MOSH-Insa-Toulouse/2023-2024-GP-Delpech_Maurel-Audry/images/Freq coupure 2eme etage.PNG

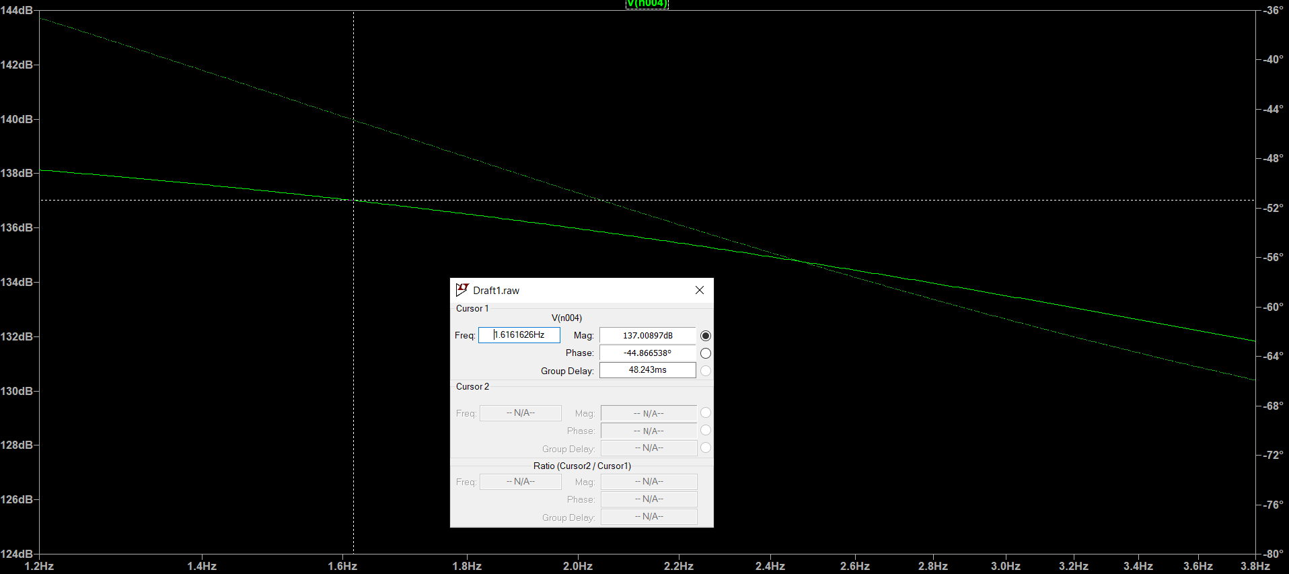
images/Freq coupure 2eme etage.PNG
